WeasalCrafter/linklite-v2/data/export/comparison_01.png

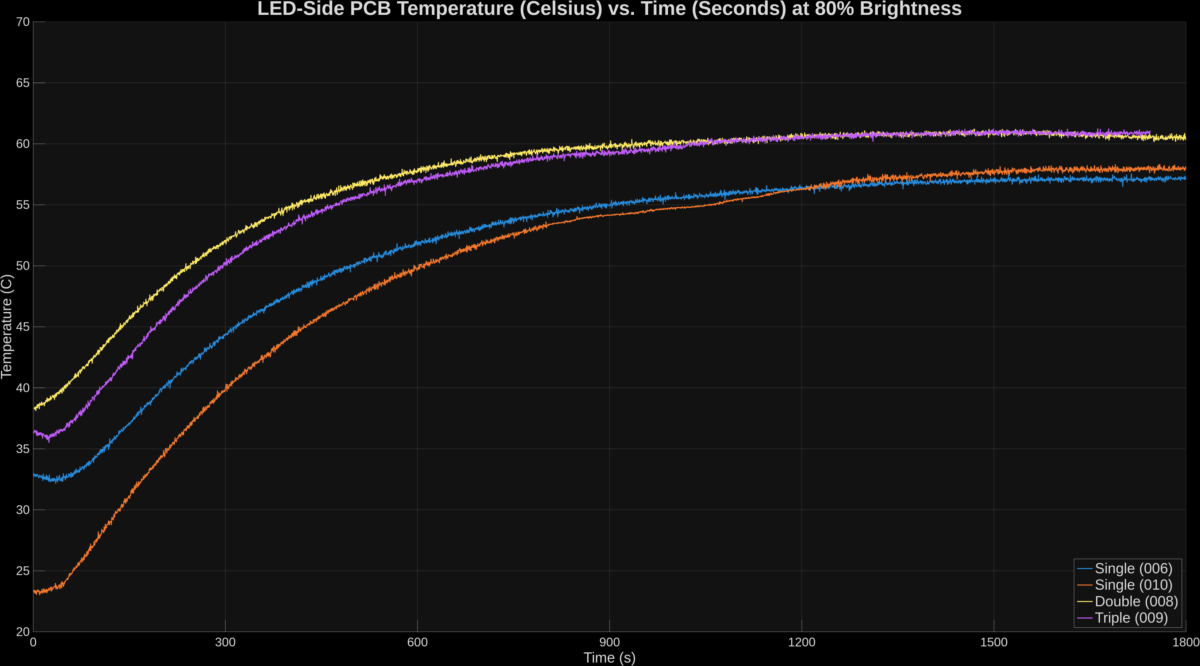
data/export/comparison_01.png
